mbuciuman/SecretAgentsSmashCompanion/src/InputModifier.hpp

#ifndef GCTRAIN_INPUTMODIFIER_HPP_
#define GCTRAIN_INPUTMODIFIER_HPP_

#include <Nintendo.h>

class InputModifier {
  public:
    virtual ~InputModifier() = 0;
    virtual void modifyInput(Gamecube_Data_t &dataToModify) = 0;
    virtual void cleanUp() = 0;
};
#endif // GCTRAIN_INPUTMODIFIER_HPP_
